balassy/star-wars-macro-keyboard/models/RightButtonStripe-v122.stl

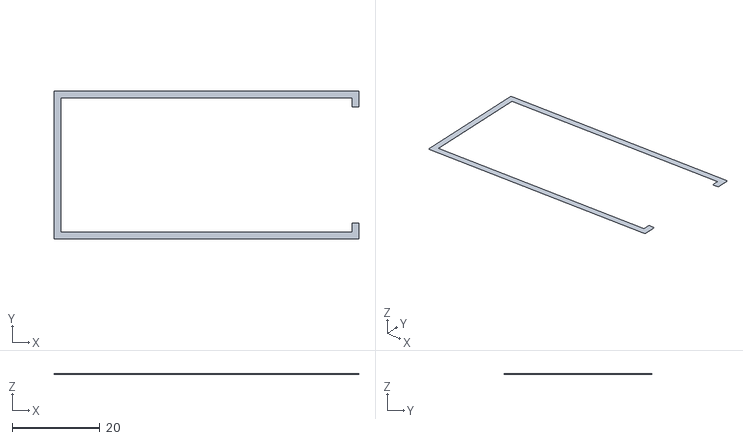
[picture p22: CAD file, 2020-11-08]
models/RightButtonStripe-v122.stl
69.5 x 33.7 x 0.2
