balassy/star-wars-macro-keyboard/models/BoardFixer-v122.stl

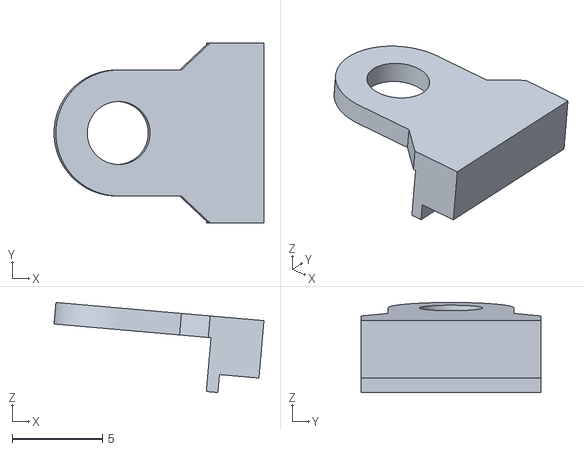
[picture p23: CAD file, 2020-11-08]
models/BoardFixer-v122.stl
11.7 x 10.0 x 5.00
