balassy/star-wars-macro-keyboard/models/PolyButtonCap-v8.step

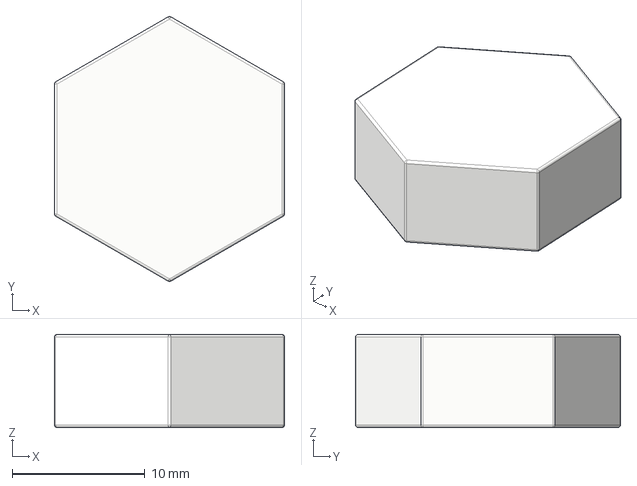
[picture p24: CAD file, 2020-11-08]
models/PolyButtonCap-v8.step
17.3 x 19.9 x 7.00 mm
