balassy/star-wars-macro-keyboard/models/RightTop-v122.stl

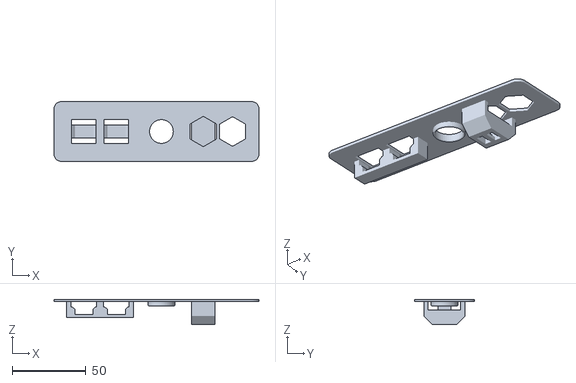
[picture p25: CAD file, 2020-11-08]
models/RightTop-v122.stl
138.8 x 40.5 x 17.2
